bschulz1701/Project-Hyena/Testing/TestingCaptures/CrystalTest.PNG

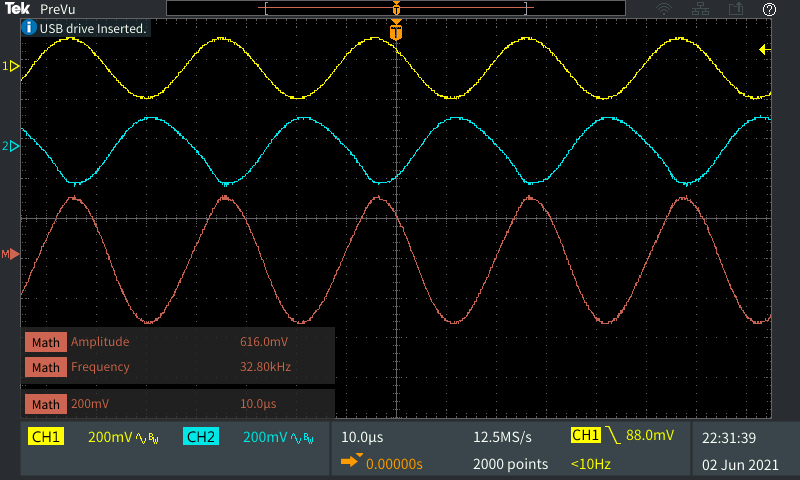
Testing/TestingCaptures/CrystalTest.PNG
