bschulz1701/Project-Hyena/Testing/TestingCaptures/TEK0000.JPG

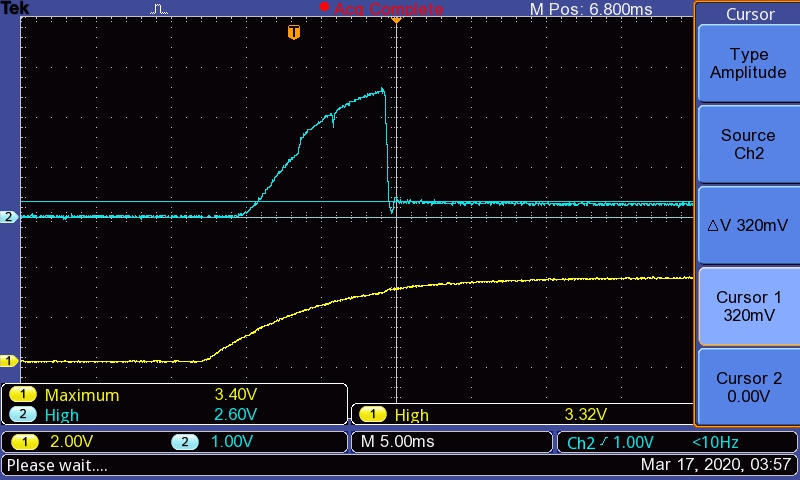
Testing/TestingCaptures/TEK0000.JPG
