bschulz1701/Project-Hyena/Testing/TestingCaptures/TEK0001.JPG

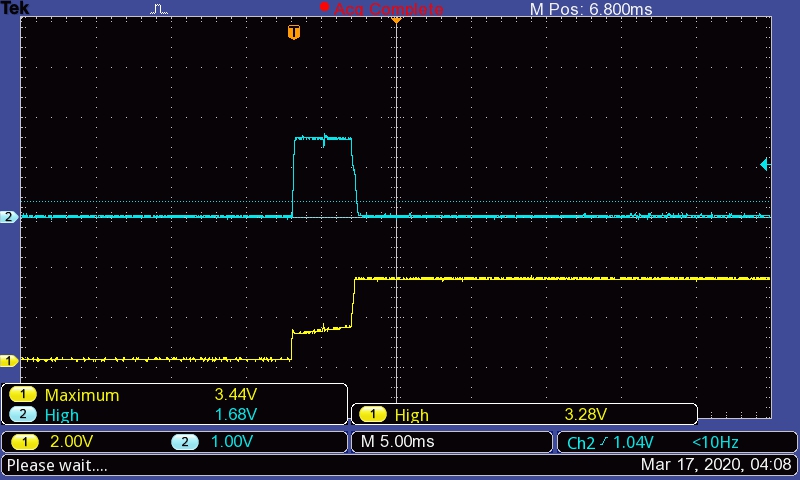
Testing/TestingCaptures/TEK0001.JPG
