bschulz1701/Project-Hyena/Testing/TestingCaptures/TEK0002.JPG

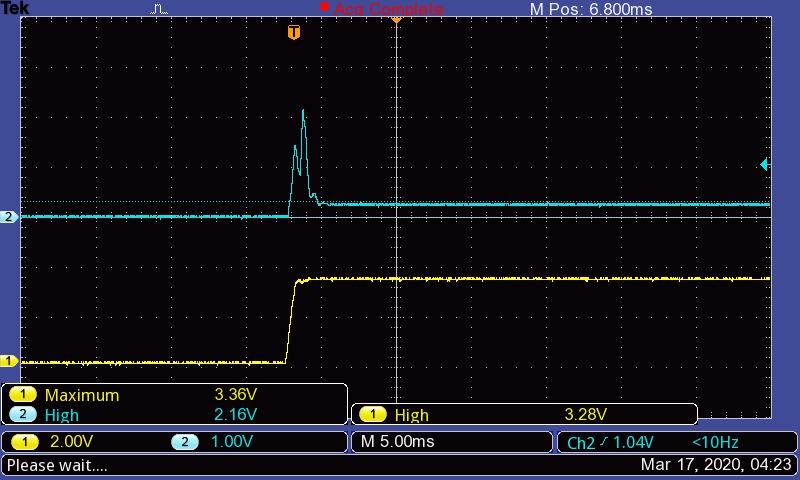
Testing/TestingCaptures/TEK0002.JPG
