bschulz1701/Project-Hyena/Testing/TestingCaptures/TEK0004.JPG

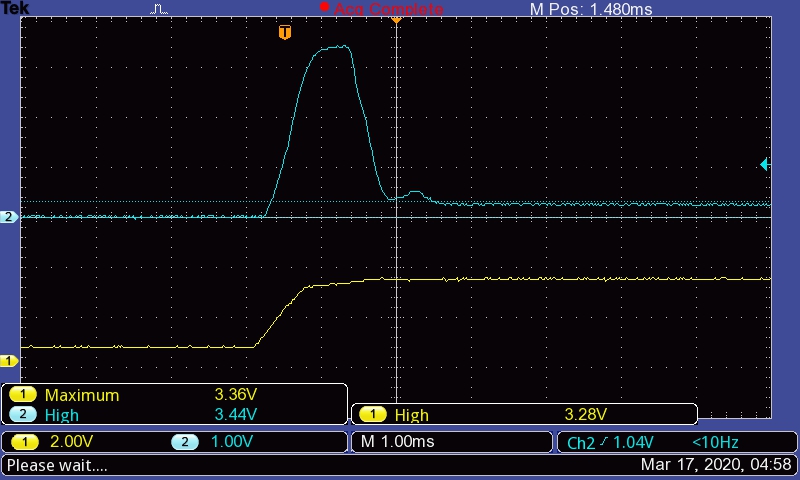
Testing/TestingCaptures/TEK0004.JPG
